Marcus10110/SolarPowerInterrupter/simulation/ndo-solar-switch.asc

C1: cap; 4.7µ
D1: zener; BZX84C10L
D2: zener; BZX84C10L
M1: pmos; BSS84
R1: res; 1.6k
R2: res; 56k
R3: res; 56k
R4: res; 10k
R6: res; 10k
R7: res; 6K
U1: BSS138
U2: BSS138
V1: voltage; 25
V2: voltage; PULSE(0 5 0 1m 1m 300m 600m 100)
Named nets: 0, Vout
.include "BSS138.lib"
.tran 1
Driver for Solar disconnect solid state relay
This disconnects the solar panel from the solar charger when AC power is enabled
